calerouxz/TemperKB-case/Images/Pictures/Temper gasket case-03.jpg

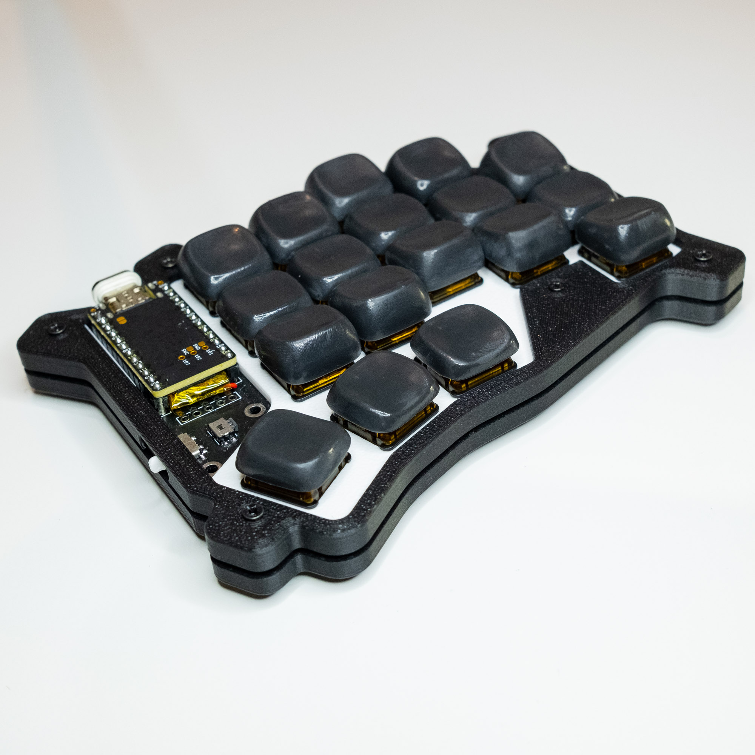
Images/Pictures/Temper gasket case-03.jpg
