calerouxz/TemperKB-case/Images/Pictures/Temper gasket case-04.jpg

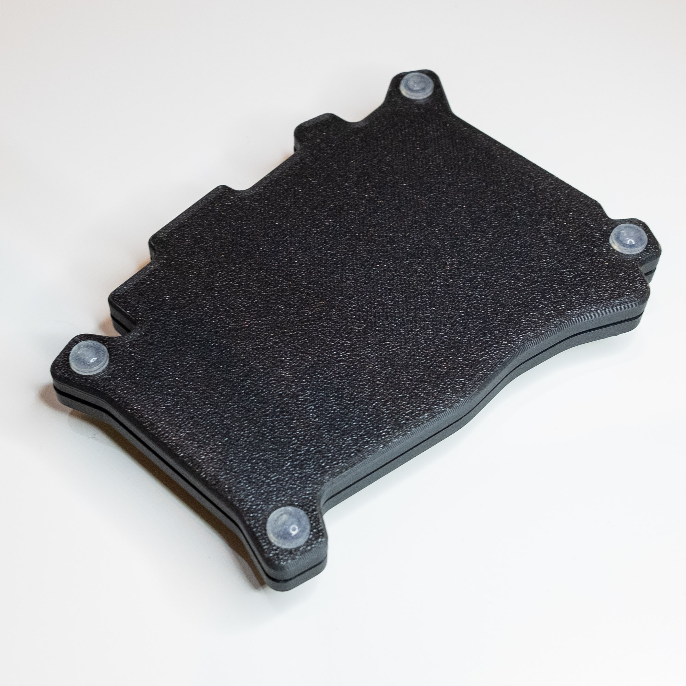
Images/Pictures/Temper gasket case-04.jpg
