calerouxz/TemperKB-case/Images/Pictures/Temper gasket case-06.jpg

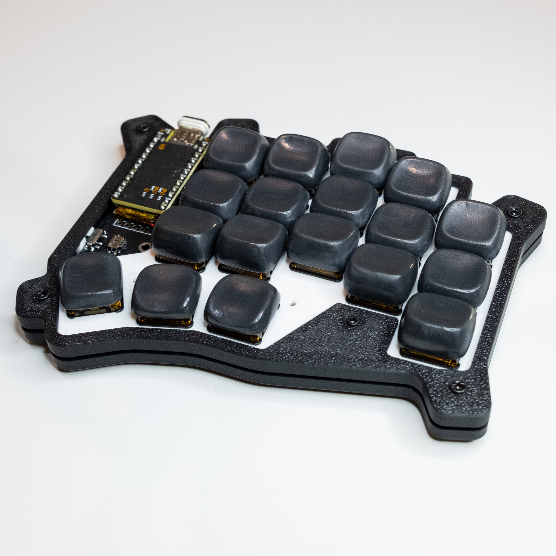
Images/Pictures/Temper gasket case-06.jpg
