calerouxz/TemperKB-case/Images/Pictures/Temper gasket case-07.jpg

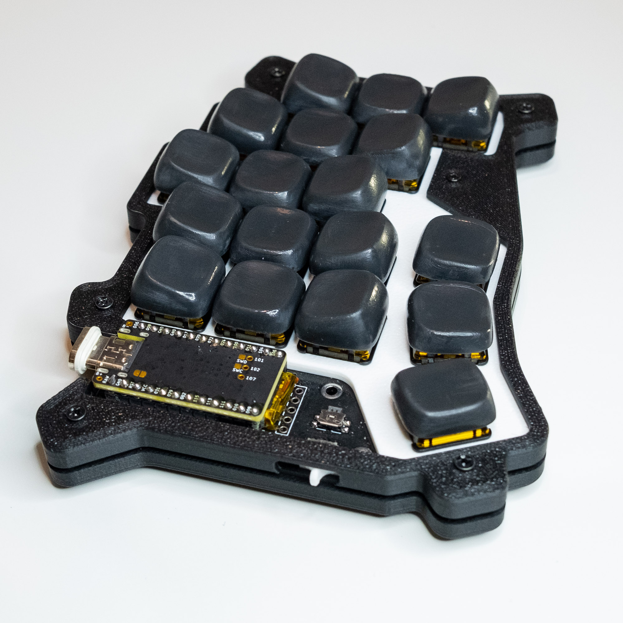
Images/Pictures/Temper gasket case-07.jpg
