calerouxz/TemperKB-case/Images/Pictures/Temper gasket case-10.jpg

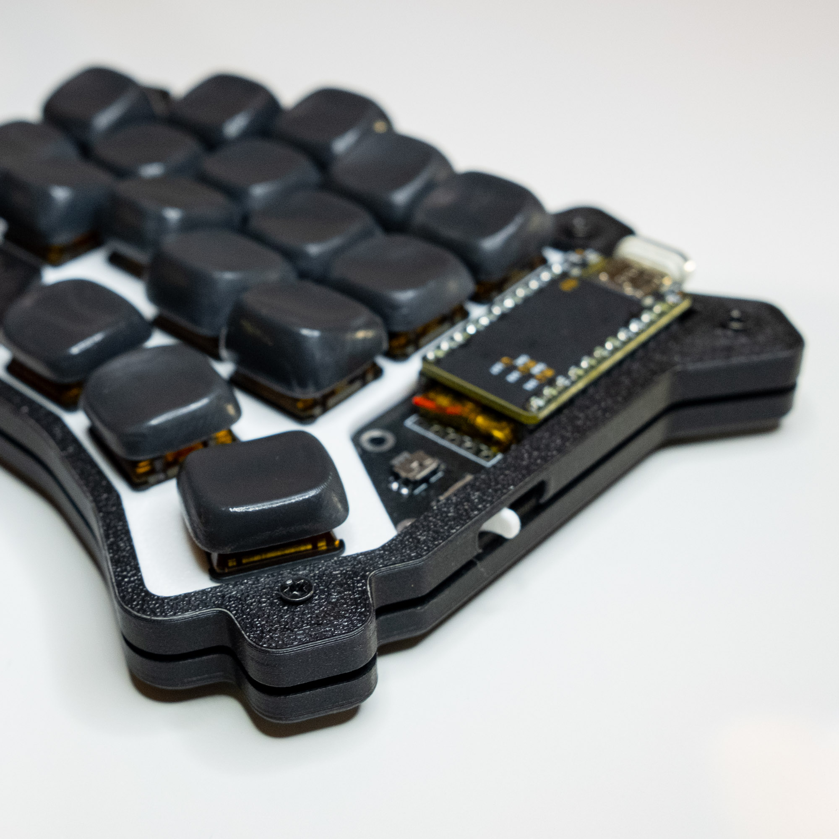
Images/Pictures/Temper gasket case-10.jpg
